DevPro13/Fall-Detection-and-Alarming-Sys/Resources/Images/IMG_20241230_154448.jpg

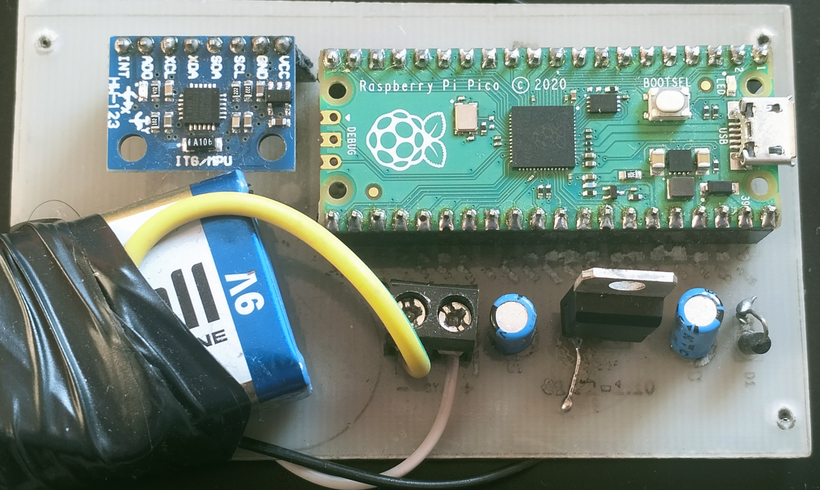
Resources/Images/IMG_20241230_154448.jpg
